ryang2856/Hand-Washer/Code_Clock/graphics.c

unsigned char menuPage[] = 
{
0x00, 0x00, 0x00, 0x00, 0x00, 0x00, 0x00, 0x00, 0x00, 0x00, 0x00, 0x00, 0x00, 0x00, 0x00, 0x00, 
0x00, 0x00, 0x00, 0x00, 0x00, 0x00, 0x00, 0x00, 0x00, 0x00, 0x00, 0x00, 0x00, 0x00, 0x00, 0x00, 
0x00, 0x00, 0x00, 0x00, 0x00, 0x00, 0x00, 0x00, 0x00, 0x00, 0x00, 0x00, 0x00, 0x00, 0x00, 0x00, 
0x00, 0x00, 0x00, 0x00, 0x00, 0x00, 0x00, 0x00, 0x00, 0x00, 0x00, 0x00, 0x00, 0x00, 0x00, 0x00, 
0x00, 0x00, 0x00, 0x00, 0x00, 0x00, 0x00, 0x00, 0x00, 0x00, 0x00, 0x00, 0x00, 0x00, 0x00, 0x00, 
0x00, 0x00, 0x00, 0x00, 0x00, 0x00, 0x00, 0x00, 0x00, 0x00, 0x00, 0x00, 0x00, 0x00, 0x00, 0x00, 
0x00, 0x00, 0x00, 0x00, 0x00, 0x00, 0x00, 0x00, 0x00, 0x00, 0x00, 0x00, 0x00, 0x00, 0x00, 0x00, 
0x00, 0x00, 0x00, 0x00, 0x00, 0x00, 0x00, 0x00, 0x00, 0x00, 0x00, 0x00, 0x00, 0x00, 0x00, 0x00, 
0x00, 0x00, 0x00, 0x00, 0x00, 0x00, 0x30, 0x00, 0x00, 0x00, 0x00, 0x00, 0x20, 0x00, 0x00, 0x00, 
0x00, 0x10, 0x10, 0x00, 0x00, 0x00, 0x30, 0x01, 0x03, 0x02, 0x00, 0x00, 0x20, 0x00, 0x00, 0x00, 
0x00, 0x10, 0x10, 0x00, 0x00, 0x00, 0x30, 0x01, 0x03, 0x06, 0x00, 0x00, 0x20, 0x00, 0x00, 0x00, 
0x00, 0x10, 0x10, 0x00, 0x00, 0x00, 0x30, 0x01, 0x87, 0x04, 0x00, 0x00, 0x20, 0x00, 0x00, 0x00, 
0x00, 0x10, 0x11, 0xf8, 0x5f, 0x07, 0xf0, 0x00, 0x85, 0x84, 0xfc, 0x36, 0x2f, 0x87, 0xc3, 0xe0, 
0x00, 0x10, 0x10, 0x0c, 0x61, 0x08, 0x70, 0x00, 0xc4, 0x8c, 0x06, 0x40, 0x30, 0x8c, 0x23, 0x00, 
0x00, 0x1f, 0xf0, 0x04, 0x40, 0x98, 0x30, 0x00, 0xcc, 0xc8, 0x02, 0x60, 0x20, 0x88, 0x13, 0x00, 
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
0x2,0x10,0x91,0x38,0x83,0x19,0x4,0x0,0x87,0x19,0x4,0x62,0x42,0x10,0x80,0x0,
0x2,0x10,0x91,0x3c,0x82,0x9,0x4,0x0,0x85,0x19,0x6,0x72,0x42,0x10,0x80,0x0,
0x2,0x10,0x9e,0x34,0x82,0x9,0xe7,0x80,0x89,0x19,0x2,0xb4,0x42,0x1f,0x80,0x0,
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
};
